BoujeeEnjinia1701/airstreet/cad/drawings/AST-DWG-001.pdf

CONCEPT, NOT FOR FABRICATION | AirStreet · github.com/BoujeeEnjinia1701/airstreet

FRONT VIEW
Scale 1:10; looking at the front (along +Y)

TOP VIEW
Scale 1:10; looking down (along -Z)

RIGHT VIEW
Scale 1:10; looking at the right side (along -X)

452

312 950

95

706 node

375
200

170

200

STREET SIDE (-Y); KERB BEYOND

POLE 140

172

PANEL TILT 40 DEG

ISOMETRIC VIEW
Not to scale; pole stub shown; seen from the front right and above, about 30 deg elevation

MAIN DIMENSIONS AND INTERFACES (MM)
Pole 80 to 200 OD (design 140); two 12.7 stainless bands 375 apart, 140 deg V-saddles
Rail 40 x 4 x 451; two 3 mm adapter plates with lightening windows carry the FieldNode lugs and bracket Cross arm 30 x 30 x 3 angle, 415 long; pod and shield hang under it on screws
FieldNode core 150 x 90 x 200, underside 3,230; 6 W panel at 40 deg
Pod 170 x 110 x 95 behind mesh, drip lid +15; FieldNode whip 15 clear of the lid
Inlet plane 3,000 above sidewalk, chain line in front view (EU 1,500 to 4,000)
Shield 8 plates 120 OD x 1.5 at 13 pitch, 200 from pole axis, 172 from pole face; T and RH probe at 3,032 M12 port A (switched 5 V): SPS30 and SHT45; port B (5 V held on): NO2 front end
Mass 3.62 kg, 3.78 kg with sun shield (R13 limit 4.0 kg); frontal area 0.139 m² (AST-CAL-001 v0.6) Third-angle; front view from the street (-Y); pole on the Z axis
REV | DESCRIPTION | DATE | BY
P1 | Preliminary GA for TRL 3 (from cad/src/model.py) | 2026-09-25 | AC
P2 | DDR-002: FieldNode back plate left off, adapter bars; notes | 2026-09-25 | AC
P3 | Layout and labels tidied | 2026-09-25 | AC
P4 | DDR-003: design for construction; saddles, plates, cross arm, pod | 2026-09-30 | AC
P5 | DDR-003 A1 lightening: 40 x 4 rail, plate windows, 1.5 shield plates | 2026-10-02 | AC
AIRSTREET | github.com/BoujeeEnjinia1701/airstreet

## General arrangement

DRAWING NO.
AST-DWG-001

REV
P5

SHEET
1 of 1

SIZE

## ANSI B

SCALE
1:10

UNITS
mm
PROJECTION | DATE
2026-10-02

DRAWN
Amish Chadha

MATERIAL / NOTES
FieldNode core per FND-BLD-001; parts per bom/bom.csv; making sketches AST-DWG-101 to 109. PRELIMINARY
Licensed CERN-OHL-S-2.0 · Design Molecule Lab · designmolecule.com | Generated from cad/src; do not edit by hand
