BoujeeEnjinia1701/airstreet/cad/drawings/AST-DWG-101.pdf

### BUILD PLAN SKETCH, PLAN NOT YET BUILT AirStreet · github.com/BoujeeEnjinia1701/airstreet

FRONT VIEW
Scale 1:5; looking at the front (along +Y)

TOP VIEW
Scale 1:5; looking down (along -Z)

RIGHT VIEW
Scale 1:5; looking at the right side (along -X)

40

4 451

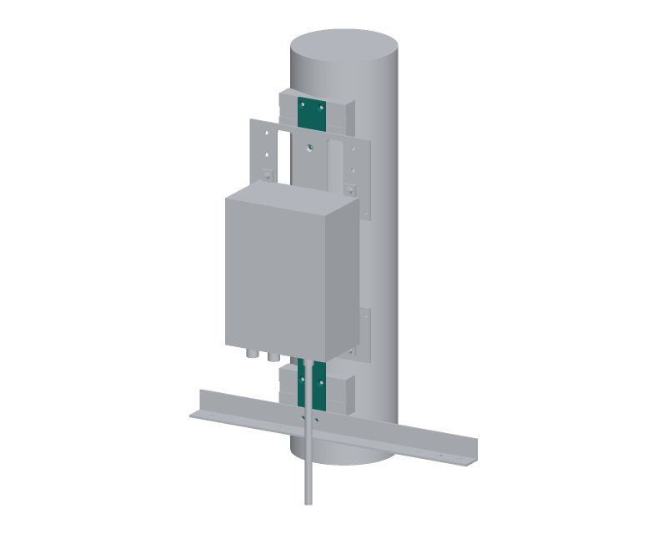
[picture p7: figure]

WHERE IT GOES
This part in colour, its neighbours in grey

HOW TO MAKE IT AND HOW IT FITS
Cut 451 mm of 40 x 4 mm flat bar; square and deburr the ends.
Heights up from the bottom end; the front is the face away from the pole. Saddle screws: 5.5 mm, 14 mm each side of centre, 67 and 442 up; countersink from the front so M5 countersunk heads sit flush.
Cross arm bolts: 5.5 mm, 10 mm each side of centre, 16.5 up.
Adapter plate bolts: 5.5 mm on the centre line, 119, 169, 316, 386 up (plain holes: the countersinks are in the plates).
The saddle centres are 51 and 426 up (375 mm apart).
Fit: saddles behind, plates and cross arm in front; see the build plan. Check: lay the plates and arm on it; every hole lines up.
REV | DESCRIPTION | DATE | BY
P1 | Making sketch for the prototype build plan | 2026-09-30 | AC
P2 | Lighter rail: 40 x 4 mm bar (was 40 x 5) | 2026-10-02 | AC
AIRSTREET | github.com/BoujeeEnjinia1701/airstreet

## AirStreet rail: making sketch

DRAWING NO.
AST-DWG-101

REV
P2

SHEET
1 of 1

SIZE

## ANSI B

SCALE
1:5

UNITS
mm
PROJECTION | DATE
2026-10-02

DRAWN
Amish Chadha

MATERIAL / NOTES
Aluminium flat bar 40 x 4 mm, 6082 or 6063 class
Licensed CERN-OHL-S-2.0 · Design Molecule Lab · designmolecule.com | Generated from cad/src; do not edit by hand
