BoujeeEnjinia1701/airstreet/cad/drawings/AST-DWG-103.pdf

### BUILD PLAN SKETCH, PLAN NOT YET BUILT AirStreet · github.com/BoujeeEnjinia1701/airstreet

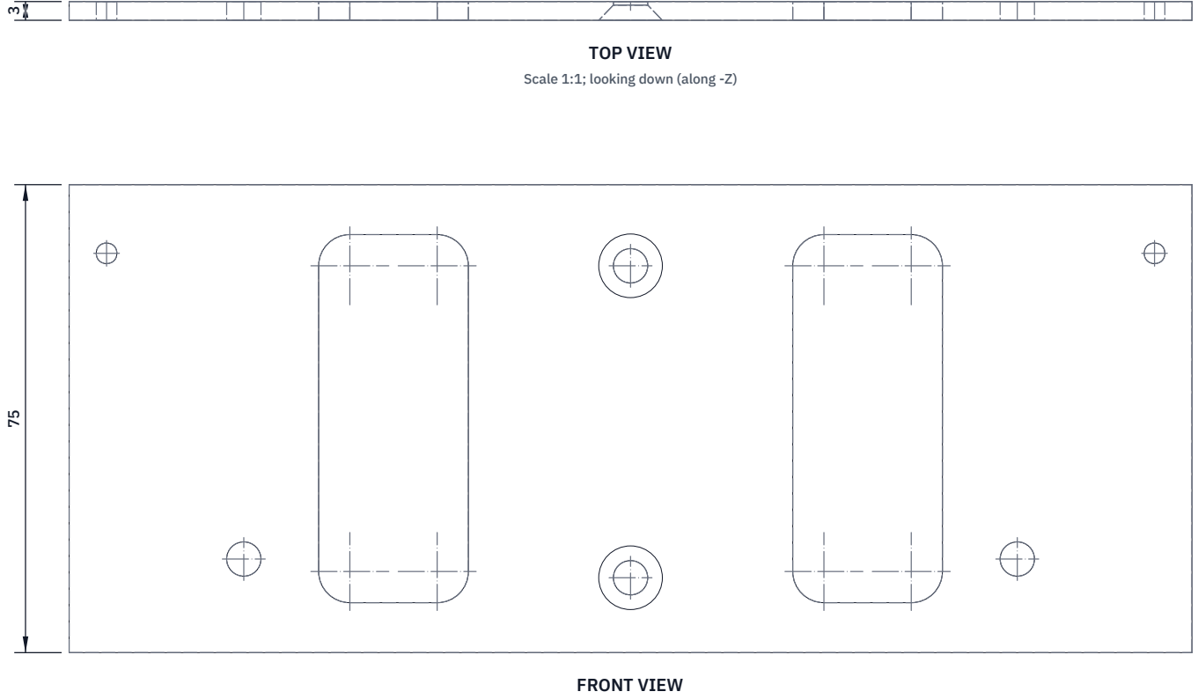
[picture p8: figure]
FRONT VIEW; TOP VIEW; Scale 1:1; looking down (along -Z)

Scale 1:1; looking at the front (along +Y)

RIGHT VIEW
Scale 1:1; looking at the right side (along -X)

180

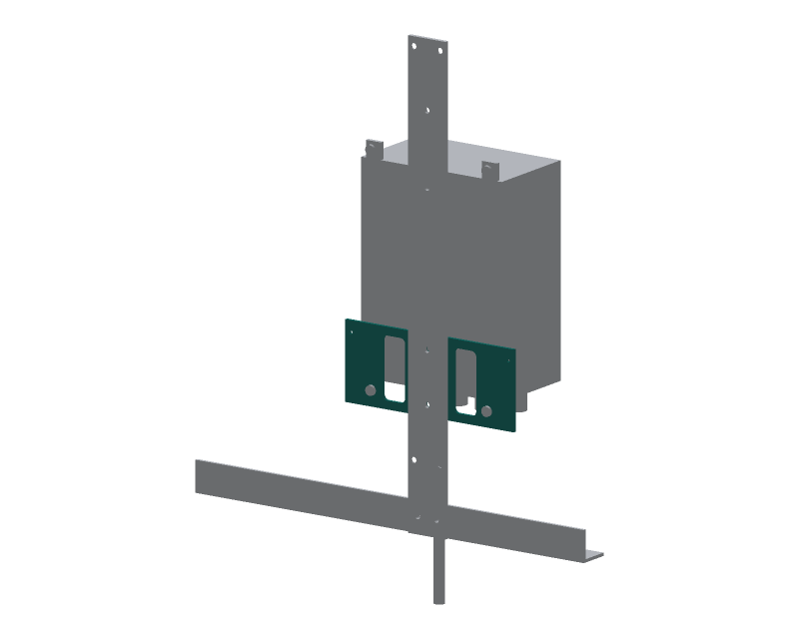
[picture p9: figure]

WHERE IT GOES
This part in colour, its neighbours in grey

HOW TO MAKE IT AND HOW IT FITS
Cut 180 x 75 mm from 3 mm sheet; round the corners about 2 mm. Heights up from the bottom edge; sideways from the centre line. Lug holes: 5.5 mm, 62 mm each side, 15 up (FieldNode's lower lugs). Sun shield holes (hot sites): drill 3.3 mm and tap M4, 84 mm each side, 64 up. Drill them on every node; they cost nothing.
Rail bolts: 5.5 mm on the centre line, 12 and 62 up, countersunk from the front so the M5 heads sit flush under the enclosure. Windows: two 24 x 59, corners R5, 26 to 50 each side, 8 to 67 up; cut out to save weight. Deburr. Holes as FieldNode's back plate. Fit: back face on the rail front, centred; enclosure back sits on its front face, bottom of the enclosure 24 above the plate's edge. Check: the lug holes are 124 mm apart, the shield holes 168 mm.
REV | DESCRIPTION | DATE | BY
P1 | Making sketch for the prototype build plan | 2026-09-30 | AC
P2 | Two lightening windows added | 2026-10-02 | AC
AIRSTREET | github.com/BoujeeEnjinia1701/airstreet

## AirStreet lower adapter plate: making sketch

DRAWING NO.
AST-DWG-103

REV
P2

SHEET
1 of 1

SIZE

## ANSI B

SCALE
1:1

UNITS
mm
PROJECTION | DATE
2026-10-02

DRAWN
Amish Chadha

MATERIAL / NOTES
Aluminium sheet 3 mm, 5052 or 6061 class
Licensed CERN-OHL-S-2.0 · Design Molecule Lab · designmolecule.com | Generated from cad/src; do not edit by hand
