BoujeeEnjinia1701/airstreet/cad/drawings/AST-DWG-104.pdf

### BUILD PLAN SKETCH, PLAN NOT YET BUILT AirStreet · github.com/BoujeeEnjinia1701/airstreet

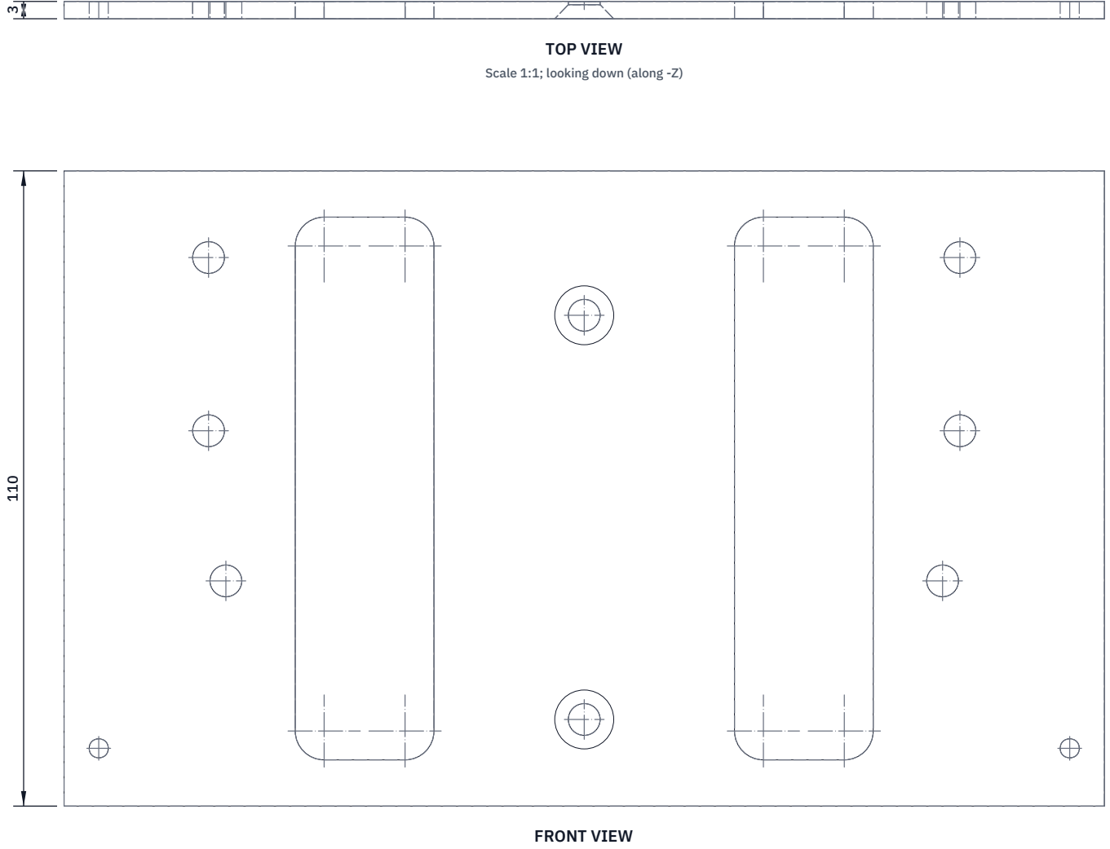
[picture p10: figure]
FRONT VIEW; TOP VIEW; Scale 1:1; looking down (along -Z)

Scale 1:1; looking at the front (along +Y)

RIGHT VIEW
Scale 1:1; looking at the right side (along -X)

180

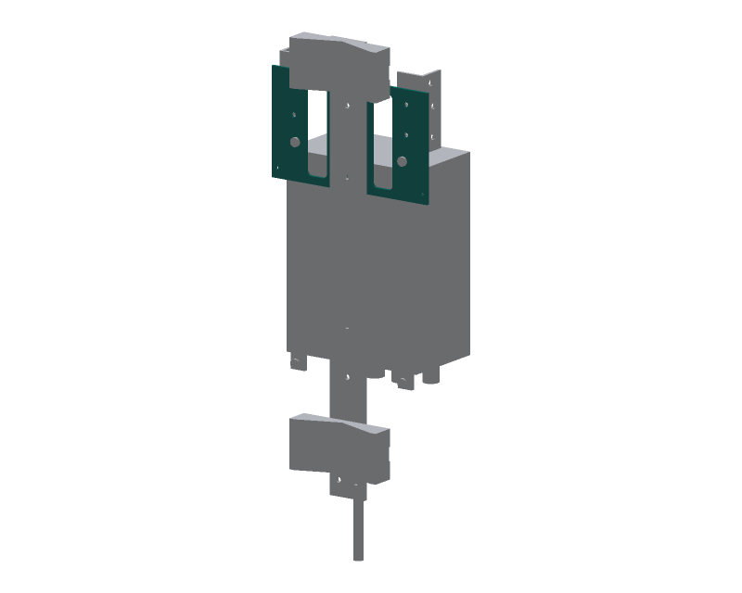
[picture p11: figure]

WHERE IT GOES
This part in colour, its neighbours in grey

HOW TO MAKE IT AND HOW IT FITS
Cut 180 x 110 mm from 3 mm sheet; round the corners about 2 mm. Heights up from the bottom edge; sideways from the centre line.
Sun shield holes (hot sites): drill 3.3 mm, tap M4; 84 each side, 10 up. Lug holes: 5.5 mm, 62 mm each side, 39 up (FieldNode's upper lugs). Plate clip holes: 5.5 mm, 65 mm each side, 65 and 95 up.
Rail bolts: 5.5 mm on the centre line, 15 and 85 up, countersunk from the front so the M5 heads sit flush.
Windows: two 24 x 94, corners R5, 26 to 50 each side, 8 to 102 up; cut out to save weight. Deburr.
The top edge is where FieldNode's back plate top edge would be. Fit: back face on the rail front; enclosure back on its lower 30 mm. Check: plate clip holes 130 apart across, 30 apart up.
REV | DESCRIPTION | DATE | BY
P1 | Making sketch for the prototype build plan | 2026-09-30 | AC
P2 | Two lightening windows added | 2026-10-02 | AC
AIRSTREET | github.com/BoujeeEnjinia1701/airstreet

## AirStreet upper adapter plate: making sketch

DRAWING NO.
AST-DWG-104

REV
P2

SHEET
1 of 1

SIZE

## ANSI B

SCALE
1:1

UNITS
mm
PROJECTION | DATE
2026-10-02

DRAWN
Amish Chadha

MATERIAL / NOTES
Aluminium sheet 3 mm, 5052 or 6061 class
Licensed CERN-OHL-S-2.0 · Design Molecule Lab · designmolecule.com | Generated from cad/src; do not edit by hand
