BoujeeEnjinia1701/airstreet/cad/drawings/AST-DWG-108.pdf

### BUILD PLAN SKETCH, PLAN NOT YET BUILT AirStreet · github.com/BoujeeEnjinia1701/airstreet

FRONT VIEW
Scale 1:2; looking at the front (along +Y)

TOP VIEW
Scale 1:2; looking down (along -Z)

RIGHT VIEW
Scale 1:2; looking at the right side (along -X)

120

120 1.5

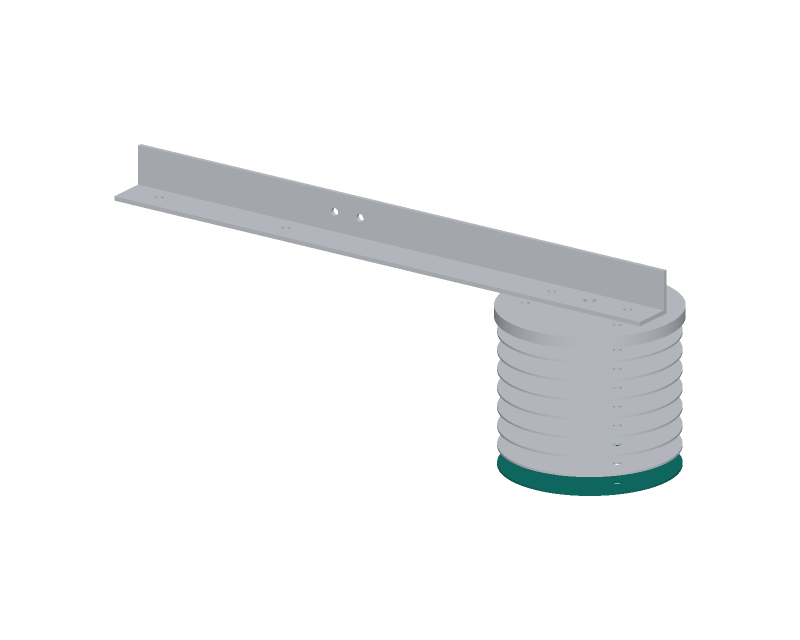
[picture p12: figure]

WHERE IT GOES
This part in colour, its neighbours in grey

HOW TO MAKE IT AND HOW IT FITS
Make eight. Ring 120 outside, 56 inside, 1.5 thick, printed flat. Three 5.5 mm holes on an 84 mm circle, 120 degrees apart; one of them on the line from the centre toward the pole.
White plastic reflects the sun; do not paint or use another colour. Make 24 spacers too: 8 mm outside, 5.5 mm bore, 21 of them 11.5 long and 3 of them 9.25 long (the top row, under the cap).
Stack: plate, 11.5 spacer, plate ... 8 plates, then the short spacers and the cap, all on three M5 rods, 13 mm from plate to plate.
Check: the stack is 13 mm pitch, plates parallel, gaps open.
REV | DESCRIPTION | DATE | BY
P1 | Making sketch for the prototype build plan | 2026-09-30 | AC
P2 | Thinner plates: 1.5 mm (was 2); spacers 11.5 and 9.25 long | 2026-10-02 | AC
AIRSTREET | github.com/BoujeeEnjinia1701/airstreet

## AirStreet shield plate (make 8): making sketch

DRAWING NO.
AST-DWG-108

REV
P2

SHEET
1 of 1

SIZE

## ANSI B

SCALE
1:2

UNITS
mm
PROJECTION | DATE
2026-10-02

DRAWN
Amish Chadha

MATERIAL / NOTES
White ASA, 3D printed, 100 % infill
Licensed CERN-OHL-S-2.0 · Design Molecule Lab · designmolecule.com | Generated from cad/src; do not edit by hand
