BoujeeEnjinia1701/airstreet/cad/drawings/AST-DWG-102.pdf

### BUILD PLAN SKETCH, PLAN NOT YET BUILT AirStreet · github.com/BoujeeEnjinia1701/airstreet

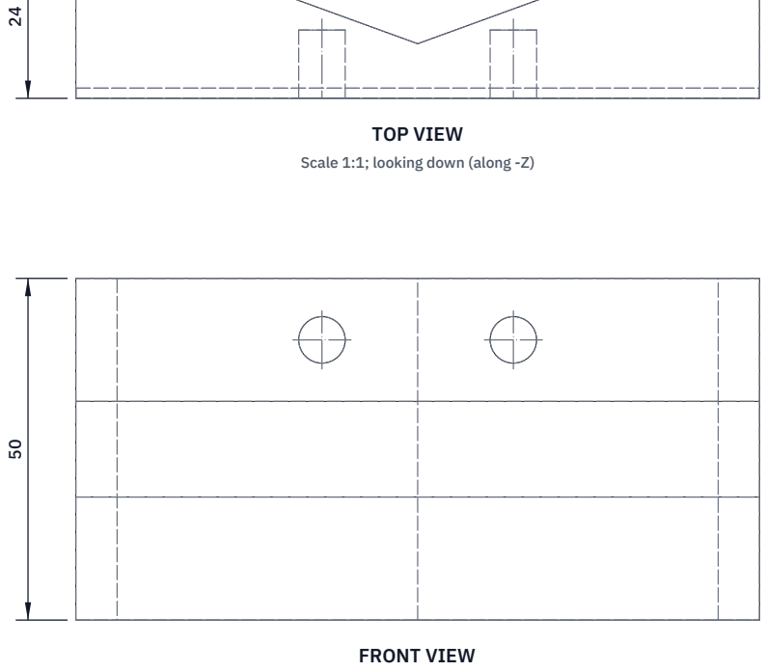
[picture p48: figure]
FRONT VIEW; TOP VIEW; Scale 1:1; looking down (along -Z)

Scale 1:1; looking at the front (along +Y)

RIGHT VIEW
Scale 1:1; looking at the right side (along -X)

100

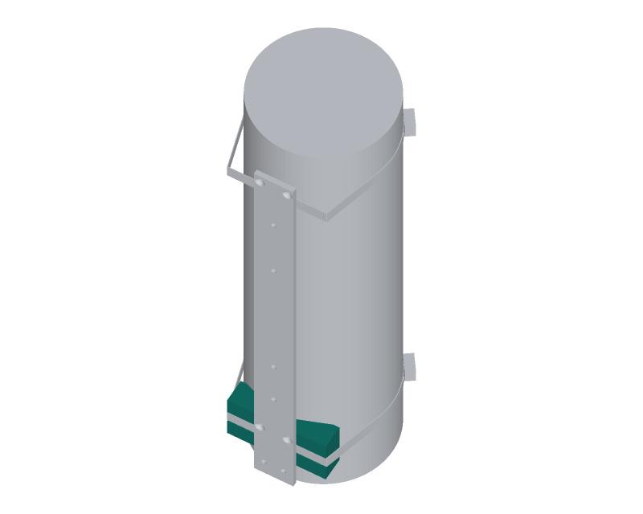
[picture p49: figure]

WHERE IT GOES
This part in colour, its neighbours in grey

HOW TO MAKE IT AND HOW IT FITS
Make two. Block 100 wide, 50 tall, 24 deep, with a 140 degree V across its full height. The flat back goes on the rail; the V faces the pole.
V: apex 8 mm in front of the back face, 87.9 mm wide at the front face. Band groove: 14 mm tall, 1.5 mm deep, across the whole back face, centred on the height. The band runs in it, between saddle and rail. Print standing on the 100 x 24 end, so the V profile is on the bed.
Two M5 heat-set inserts, 6.8 mm holes 10 deep in the back face,
14 mm each side of centre and 16 mm above the middle (lower saddle) or below it (upper saddle): print one, turn the other over.
Fit: two M5 x 16 countersunk screws from the front of the rail.
A 140 mm pole touches the V faces 24 mm each side of centre; a 200 mm pole 34 mm; an 80 mm pole 14 mm. Never on the V's edges.
Check: on a pole or tube it must not rock.
REV | DESCRIPTION | DATE | BY
P1 | Making sketch for the prototype build plan | 2026-09-30 | AC
AIRSTREET | github.com/BoujeeEnjinia1701/airstreet

## AirStreet V-saddle (make 2): making sketch

DRAWING NO.
AST-DWG-102

REV
P1

SHEET
1 of 1

SIZE

## ANSI B

SCALE
1:1

UNITS
mm
PROJECTION | DATE
2026-09-30

DRAWN
Amish Chadha

MATERIAL / NOTES
ASA, 3D printed, 6 walls, 40 % infill
Licensed CERN-OHL-S-2.0 · Design Molecule Lab · designmolecule.com | Generated from cad/src; do not edit by hand
