BoujeeEnjinia1701/airstreet/cad/drawings/AST-DWG-105.pdf

### BUILD PLAN SKETCH, PLAN NOT YET BUILT AirStreet · github.com/BoujeeEnjinia1701/airstreet

FRONT VIEW
Scale 1:5; looking at the front (along +Y)

TOP VIEW
Scale 1:5; looking down (along -Z)

RIGHT VIEW
Scale 1:5; looking at the right side (along -X)

415

30 30

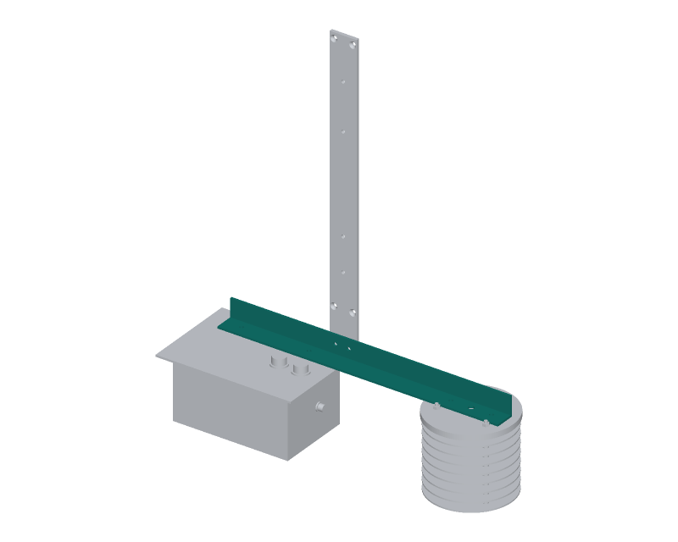
[picture p50: figure]

WHERE IT GOES
This part in colour, its neighbours in grey

HOW TO MAKE IT AND HOW IT FITS
Cut 415 mm of 30 x 30 x 3 angle; square and deburr the ends. Positions from the left end (seen from the street).
Upright leg (goes on the rail): two 5.5 mm holes at 155 and 175, 16.5 mm up from the underside of the flat leg.
Flat leg (points to the street): 15 mm in front of the back face: pod screws 5.5 mm at 25 and 125; probe tube 8 mm at 365; cap screws 5.5 mm at 335 and 395.
Fit: upright leg flat on the rail front, its underside 451 mm below the rail's top end (flush with the rail's bottom end); two M5 bolts, heads behind the rail, nyloc nuts inside the angle.
The pod and the shield cap hang under the flat leg on M5 screws put in from above.
Check: the flat leg is level when the rail is upright.
REV | DESCRIPTION | DATE | BY
P1 | Making sketch for the prototype build plan | 2026-09-30 | AC
AIRSTREET | github.com/BoujeeEnjinia1701/airstreet

## AirStreet cross arm: making sketch

DRAWING NO.
AST-DWG-105

REV
P1

SHEET
1 of 1

SIZE

## ANSI B

SCALE
1:5

UNITS
mm
PROJECTION | DATE
2026-09-30

DRAWN
Amish Chadha

MATERIAL / NOTES
Aluminium equal angle 30 x 30 x 3 mm, 6063 class
Licensed CERN-OHL-S-2.0 · Design Molecule Lab · designmolecule.com | Generated from cad/src; do not edit by hand
