BoujeeEnjinia1701/airstreet/cad/drawings/AST-DWG-106.pdf

### BUILD PLAN SKETCH, PLAN NOT YET BUILT AirStreet · github.com/BoujeeEnjinia1701/airstreet

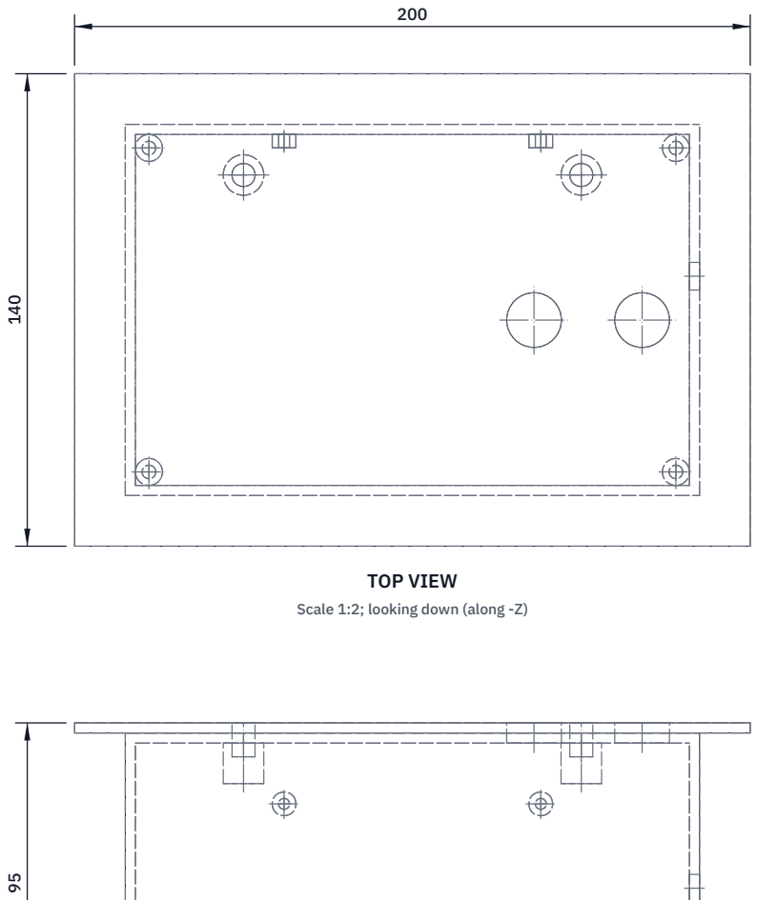
[picture p51: figure]
TOP VIEW; Scale 1:2; looking down (along -Z)
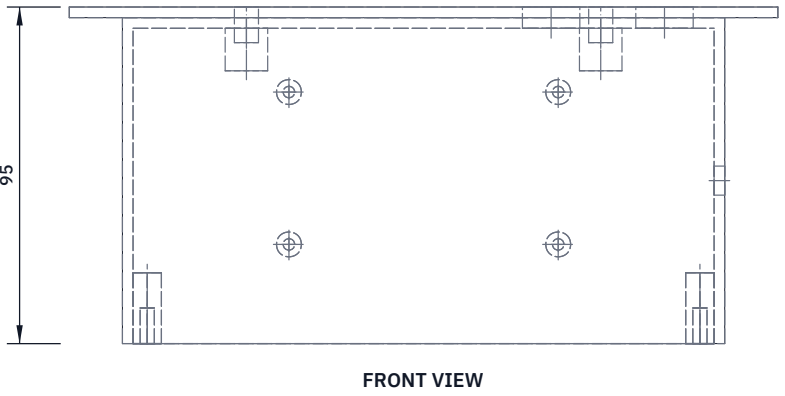
[picture p52: figure]
FRONT VIEW

Scale 1:2; looking at the front (along +Y)

RIGHT VIEW
Scale 1:2; looking at the right side (along -X)

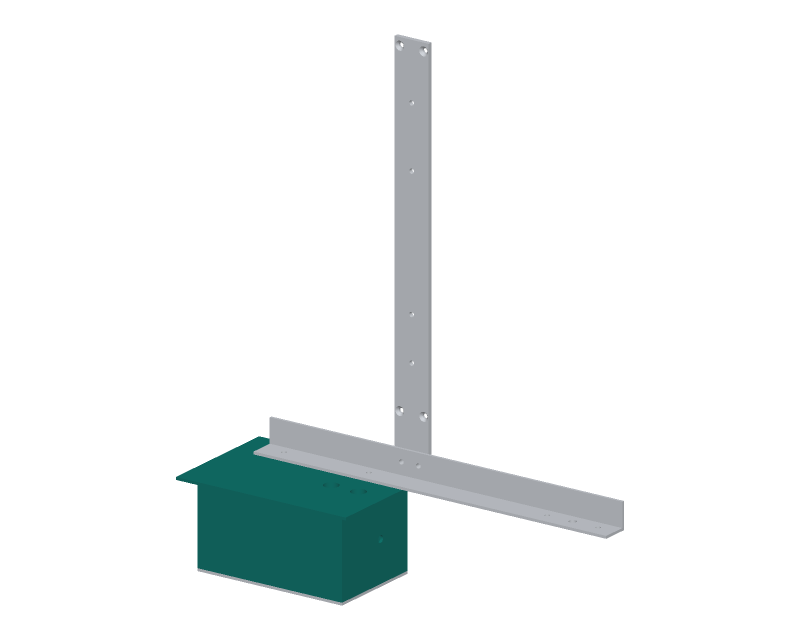
[picture p53: figure]

WHERE IT GOES
This part in colour, its neighbours in grey

HOW TO MAKE IT AND HOW IT FITS
Outside 170 wide, 110 deep, 92 tall (walls and roof 3 mm), open at the bottom; drip lid 200 x 140 x 3 on top. Print upside down, lid on the bed. Corner bosses: four 8 mm, 20 tall at the open edge, 7 mm in from the sides and ends; M3 heat-set inserts for the sensor floor screws. Hanging bosses: two 12 mm inside the roof, 50 each side of centre,
15 from the back face; M5 inserts put in from the top of the lid.
Roof glands: two 16.2 mm holes, 58 from the back face, 36 and 68 right of centre (under FieldNode's ports A and B).
Probe socket: 8.2 mm hole in the right wall, 45 from the back face,
46 above the open edge.
Back wall: four 7 mm bosses, 4 tall, M3 inserts, 76 apart across and 43 apart up, for the front end standoffs.
Check: the floor fits the open edge all round; inserts square.
REV | DESCRIPTION | DATE | BY
P1 | Making sketch for the prototype build plan | 2026-09-30 | AC
AIRSTREET | github.com/BoujeeEnjinia1701/airstreet

## AirStreet pod shell: making sketch

DRAWING NO.
AST-DWG-106

REV
P1

SHEET
1 of 1

SIZE

## ANSI B

SCALE
1:2

UNITS
mm
PROJECTION | DATE
2026-09-30

DRAWN
Amish Chadha

MATERIAL / NOTES
ASA, 3D printed, white or light grey, 4 walls
Licensed CERN-OHL-S-2.0 · Design Molecule Lab · designmolecule.com | Generated from cad/src; do not edit by hand
