BoujeeEnjinia1701/airstreet/cad/drawings/AST-DWG-107.pdf

### BUILD PLAN SKETCH, PLAN NOT YET BUILT AirStreet · github.com/BoujeeEnjinia1701/airstreet

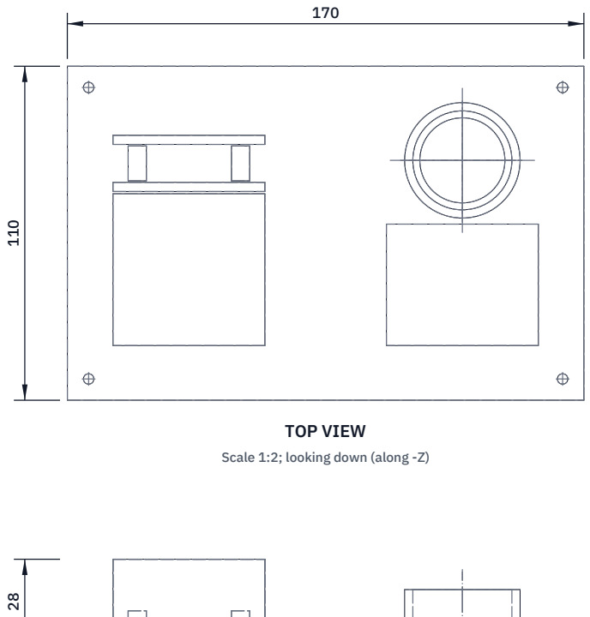
[picture p54: figure]
TOP VIEW; Scale 1:2; looking down (along -Z)

FRONT VIEW
Scale 1:2; looking at the front (along +Y)

RIGHT VIEW
Scale 1:2; looking at the right side (along -X)

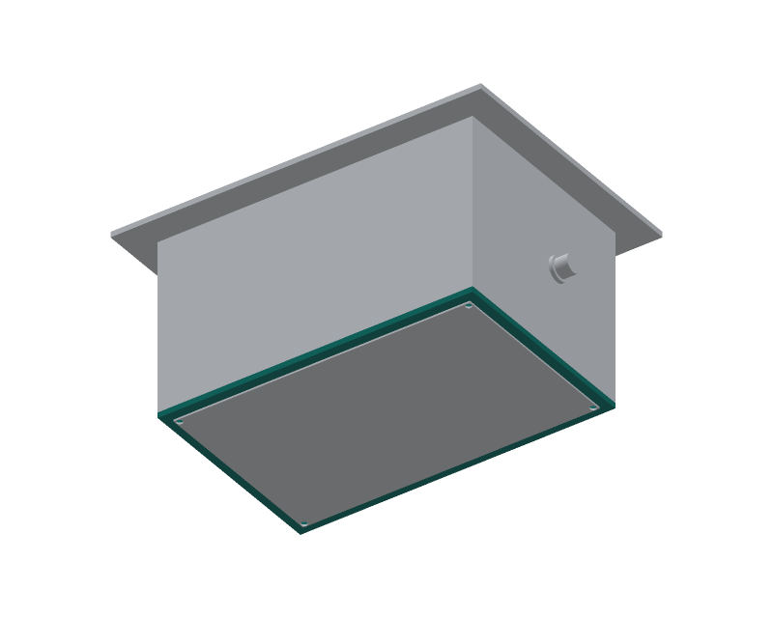
[picture p55: figure]

WHERE IT GOES
This part in colour, its neighbours in grey

HOW TO MAKE IT AND HOW IT FITS
Plate 170 x 110 x 3, printed flat with its features standing up. Inlet slots: 50 x 50 centred 45 left and 12 forward of centre;
50 x 40 centred 45 right and 17 forward of centre.
PM sensor cradle, 45 left and 23 back of centre: two ribs 50 long, 3 thick, 25 tall, 12.5 apart inside; two pads 6 wide, 8 tall, 34
apart, between the ribs. The sensor stands on the pads, inlet down. NO2 sensor: 28 mm window 45 right and 24 back of centre, inside a collar 38 outside, 32.6 inside, 15 tall. The sensor sits face down. Corner holes 3.4 mm, 78 each side and 48 forward and back of centre. Mesh: cut stainless insect mesh 160 x 100; punch the four corner holes; it goes under the floor, held by the four M3 screws.
Check: both sensors drop in without force; the floor sits flat.
REV | DESCRIPTION | DATE | BY
P1 | Making sketch for the prototype build plan | 2026-09-30 | AC
AIRSTREET | github.com/BoujeeEnjinia1701/airstreet

## AirStreet pod sensor floor: making sketch

DRAWING NO.
AST-DWG-107

REV
P1

SHEET
1 of 1

SIZE

## ANSI B

SCALE
1:2

UNITS
mm
PROJECTION | DATE
2026-09-30

DRAWN
Amish Chadha

MATERIAL / NOTES
ASA, 3D printed, 100 % infill
Licensed CERN-OHL-S-2.0 · Design Molecule Lab · designmolecule.com | Generated from cad/src; do not edit by hand
