BoujeeEnjinia1701/airstreet/cad/drawings/AST-DWG-109.pdf

### BUILD PLAN SKETCH, PLAN NOT YET BUILT AirStreet · github.com/BoujeeEnjinia1701/airstreet

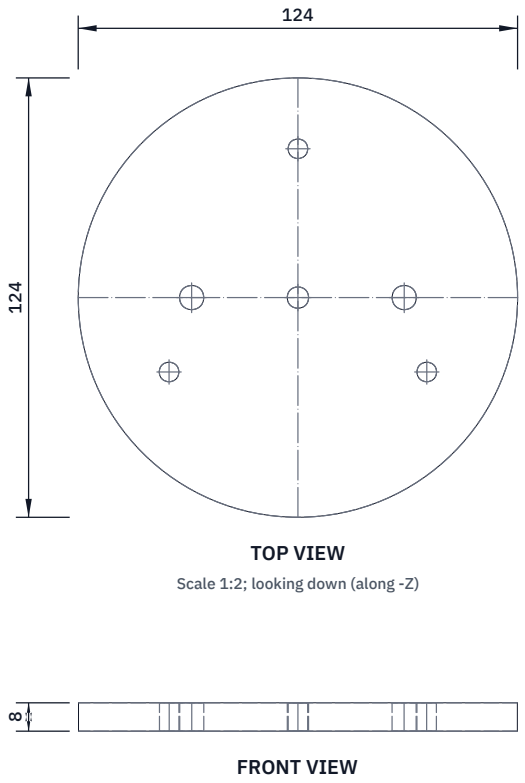
[picture p56: figure]
FRONT VIEW; TOP VIEW; Scale 1:2; looking down (along -Z)

Scale 1:2; looking at the front (along +Y)

RIGHT VIEW
Scale 1:2; looking at the right side (along -X)

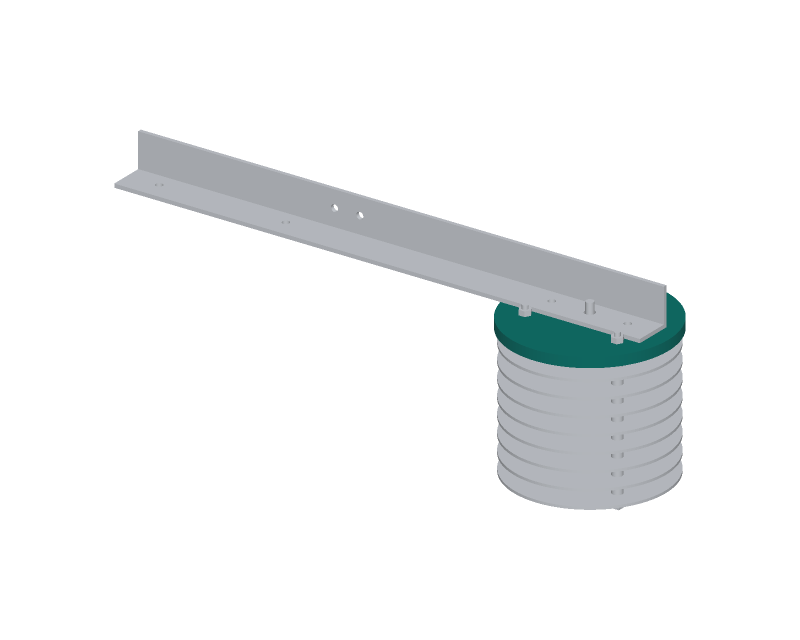
[picture p57: figure]

WHERE IT GOES
This part in colour, its neighbours in grey

HOW TO MAKE IT AND HOW IT FITS
Cap: disc 124 x 8, printed flat. A 6 mm hole at the centre for the probe tube; three 5.5 mm holes on the 84 mm circle (as the plates). Two M5 heat-set inserts in the top face, 30 each side of centre on the line along the cross arm: 6.8 mm holes, 8 deep.
Probe tube: cut 76 mm of 6 mm aluminium tube; deburr inside. Thread the 4-core probe lead up through it; glue the SHT45 board to the lower end with neutral-cure silicone, sensor facing down.
Fit: the tube goes up through the cap and the arm's 8 mm hole; the board then hangs 57 mm below the cap, in the middle of the stack. A bead of silicone holds the tube in the cap.
Check: the board does not touch any plate (19 mm clear).
REV | DESCRIPTION | DATE | BY
P1 | Making sketch for the prototype build plan | 2026-09-30 | AC
AIRSTREET | github.com/BoujeeEnjinia1701/airstreet

## AirStreet shield cap and probe tube: making sketch

DRAWING NO.
AST-DWG-109

REV
P1

SHEET
1 of 1

SIZE

## ANSI B

SCALE
1:2

UNITS
mm
PROJECTION | DATE
2026-09-30

DRAWN
Amish Chadha

MATERIAL / NOTES
White ASA, 3D printed; aluminium tube 6 mm
Licensed CERN-OHL-S-2.0 · Design Molecule Lab · designmolecule.com | Generated from cad/src; do not edit by hand
