BoujeeEnjinia1701/airstreet/cad/drawings/AST-DWG-001.png

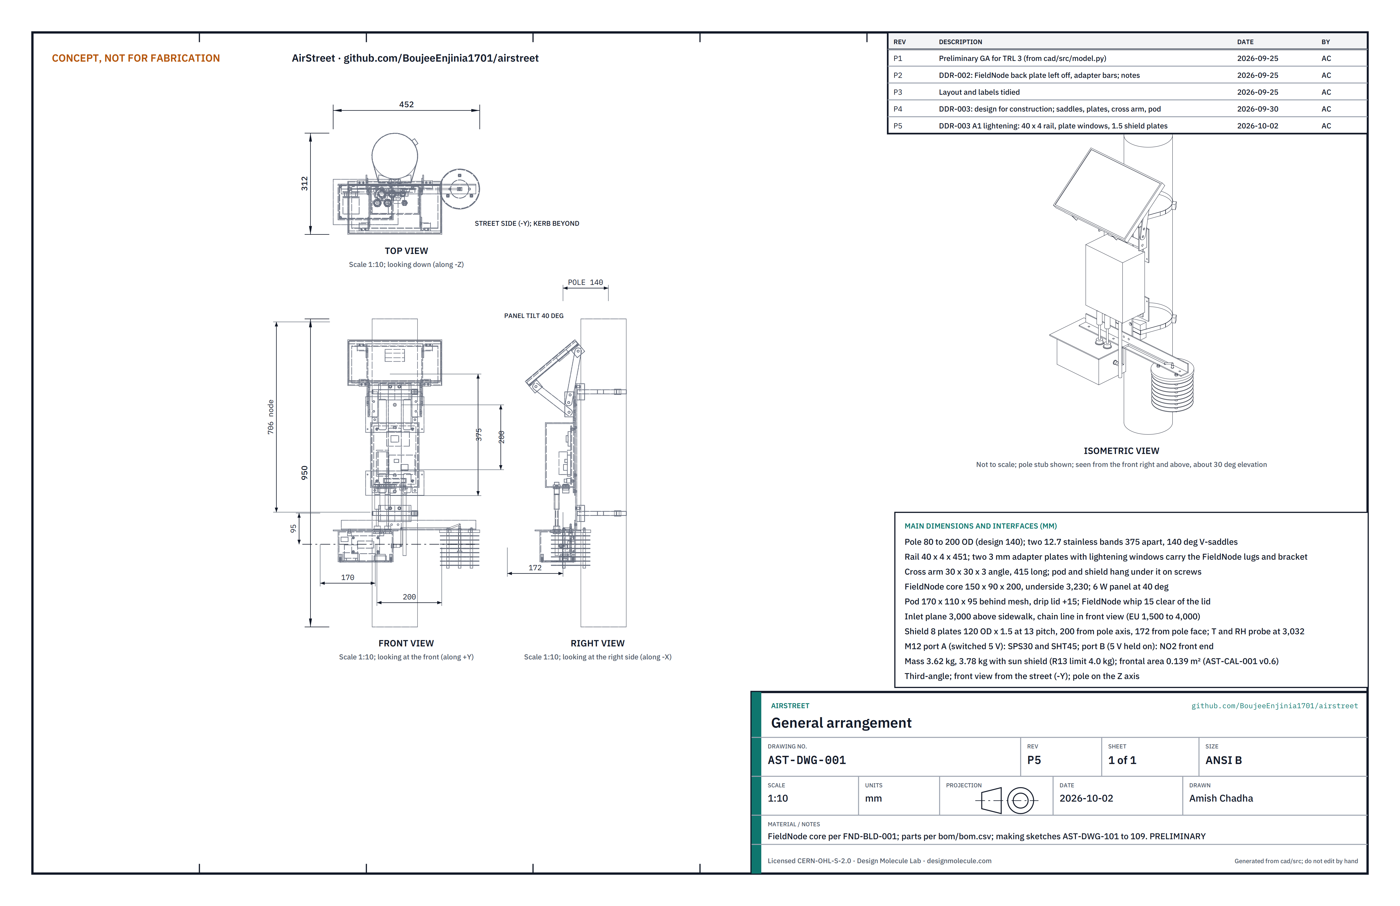
cad/drawings/AST-DWG-001.png
