BoujeeEnjinia1701/airstreet/media/card.png

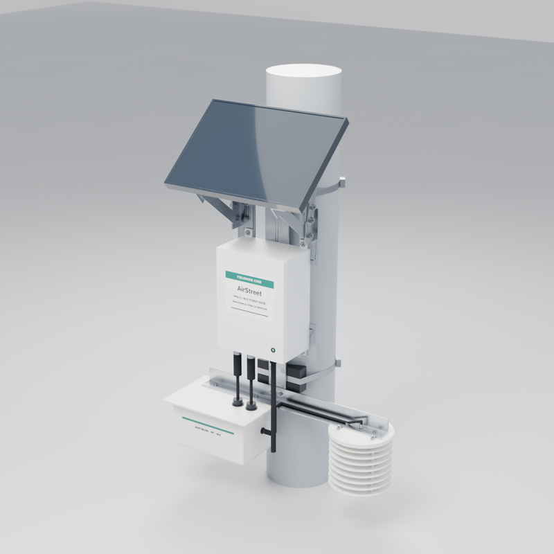
media/card.png
