BoujeeEnjinia1701/airstreet/media/render-detail.png

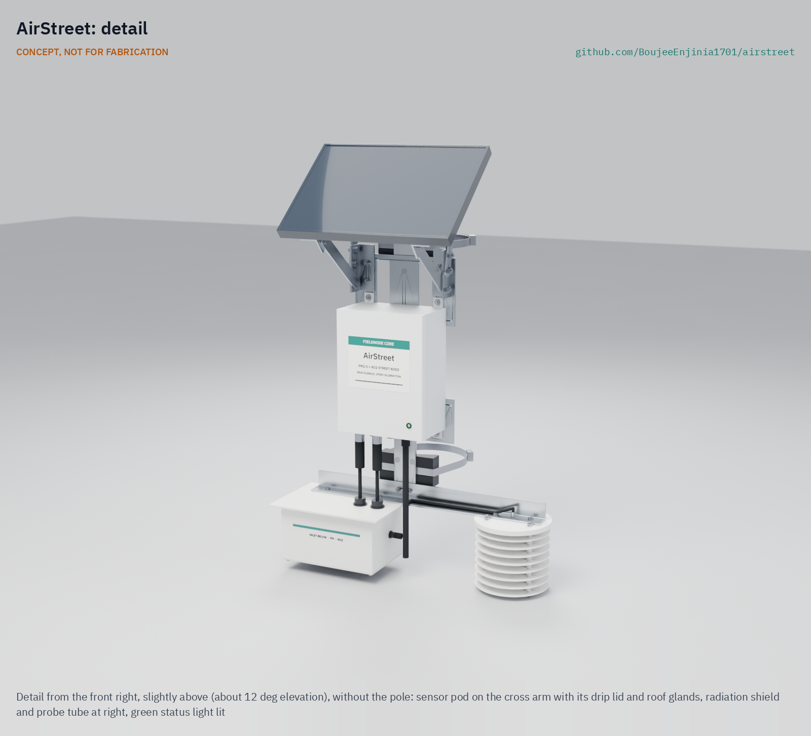
media/render-detail.png
