BoujeeEnjinia1701/airstreet/media/render-exploded.png

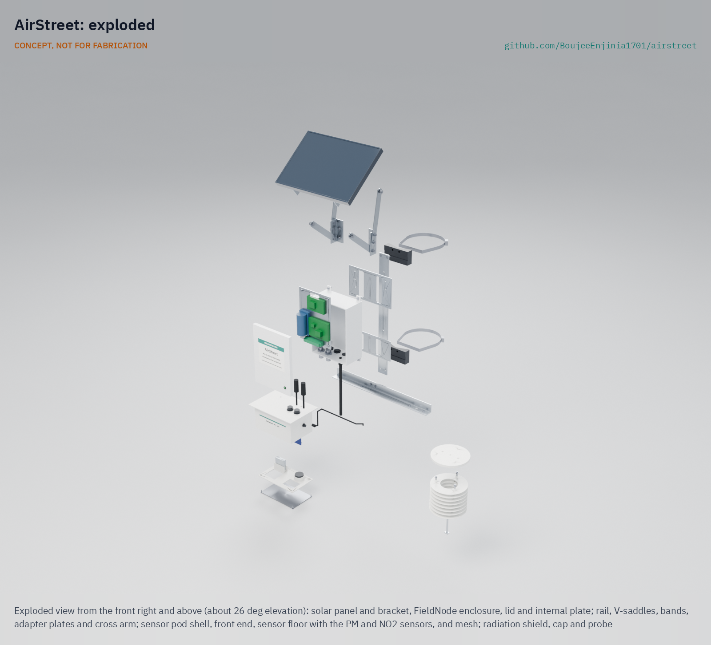
media/render-exploded.png
