BoujeeEnjinia1701/airstreet/media/social-preview.png

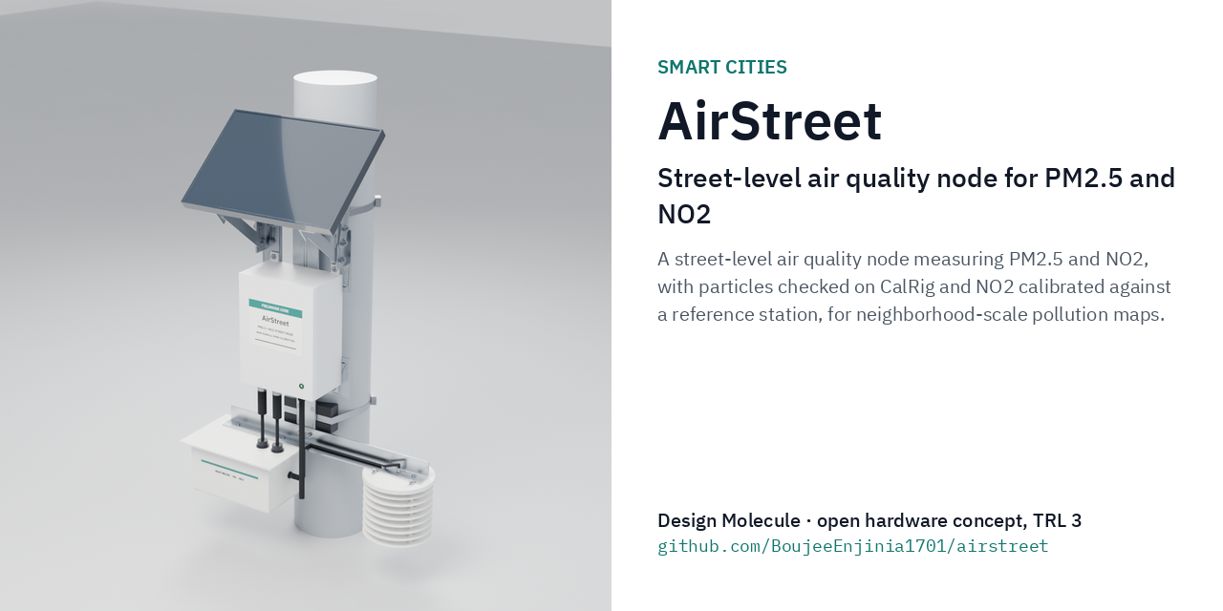
media/social-preview.png
